twartzek/watermeter/test/2026-09-08_12-16-03.jpg

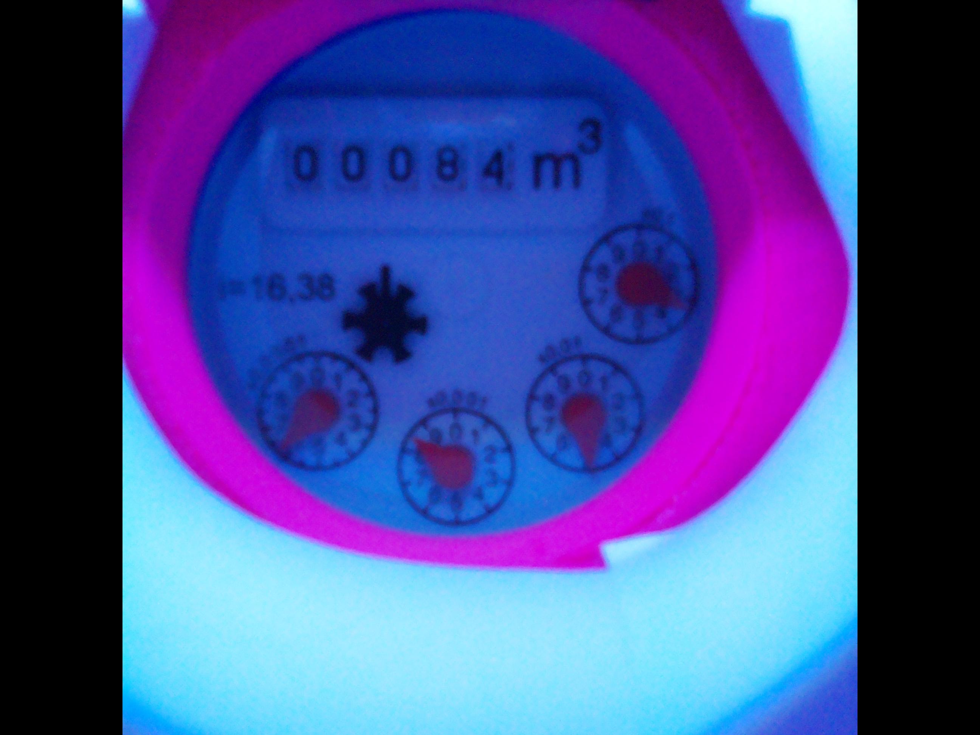
test/2026-09-08_12-16-03.jpg
